trilu2000/HB-CDL-6/Bilder/IMG_20201105_100321.jpg

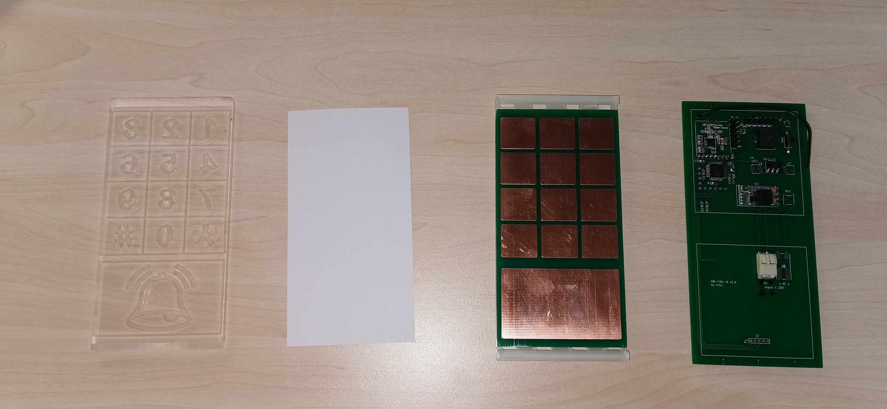
Bilder/IMG_20201105_100321.jpg
