trilu2000/HB-CDL-6/Bilder/IMG_20201105_100423.jpg

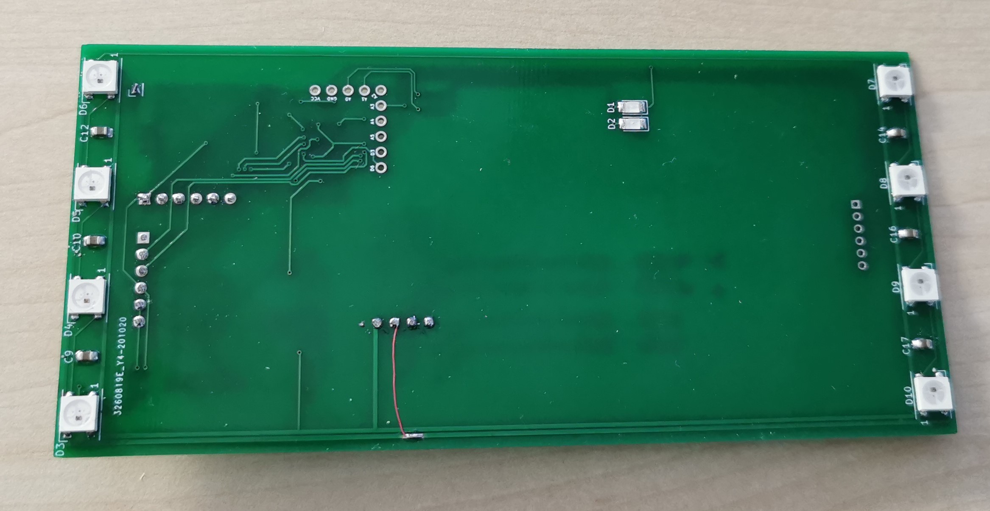
Bilder/IMG_20201105_100423.jpg
