trilu2000/HB-CDL-6/Bilder/IMG_20201105_101753.jpg

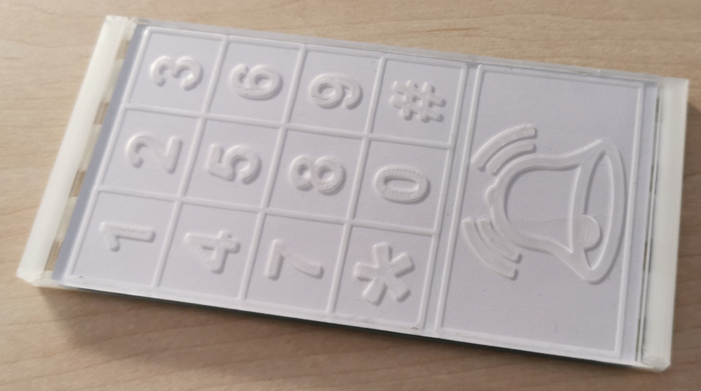
Bilder/IMG_20201105_101753.jpg
