trilu2000/HB-CDL-6/Bilder/IMG_20201106_141219.jpg

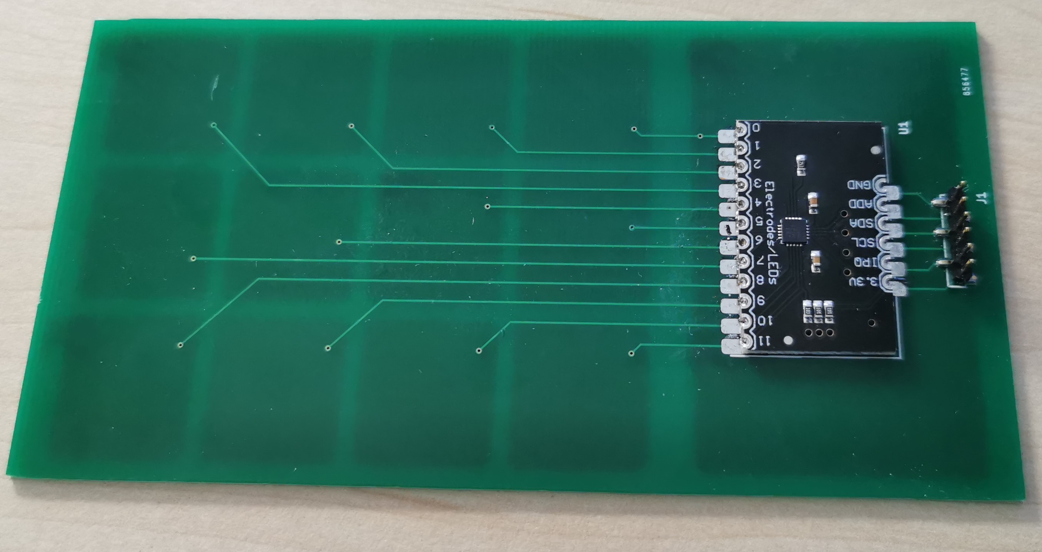
Bilder/IMG_20201106_141219.jpg
