trilu2000/HB-CDL-6/Bilder/IMG_20201106_154348.jpg

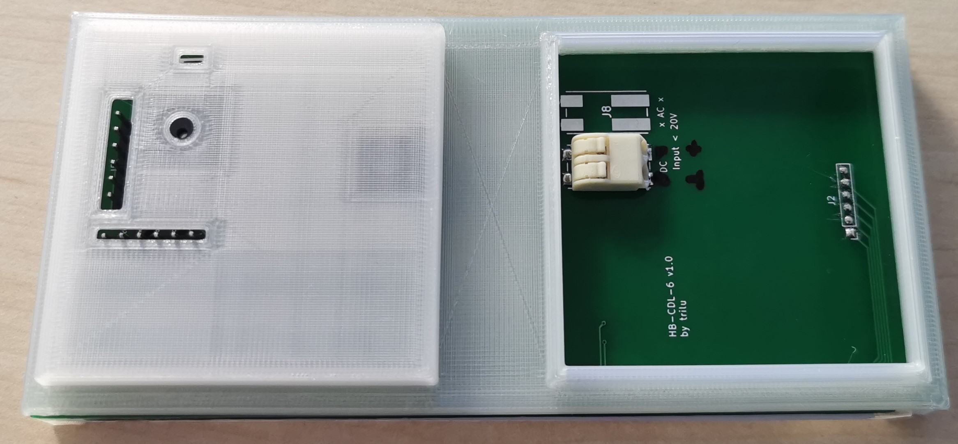
Bilder/IMG_20201106_154348.jpg
