trilu2000/HB-CDL-6/Bilder/IMG_20201106_154539.jpg

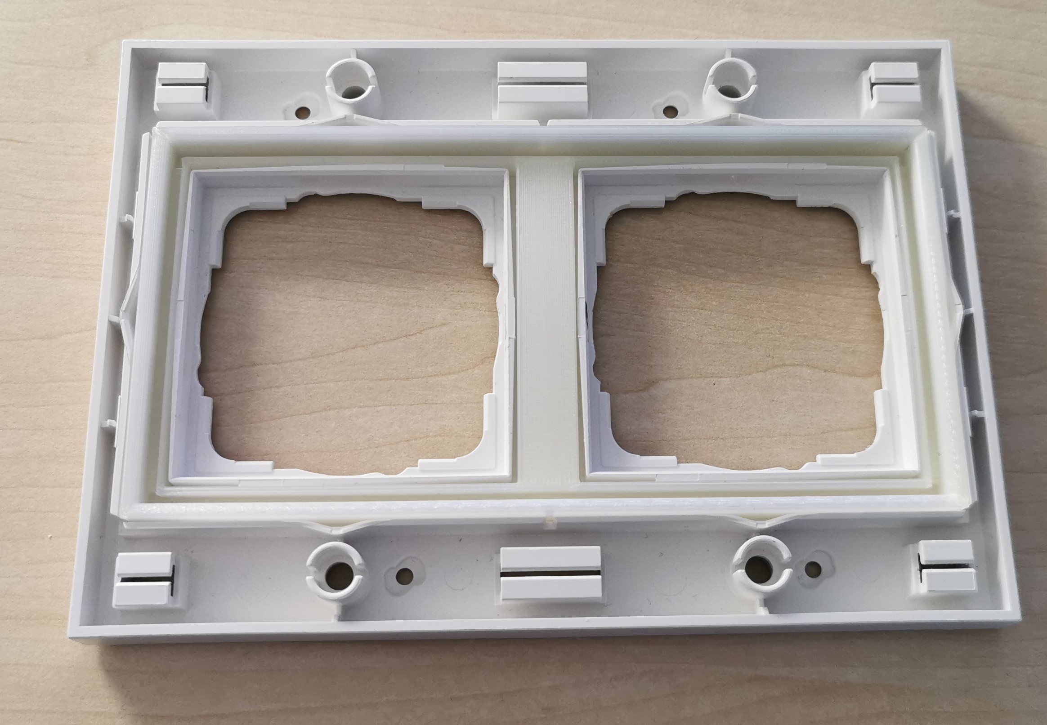
Bilder/IMG_20201106_154539.jpg
