trilu2000/HB-CDL-6/Bilder/IMG_20201109_151858.jpg

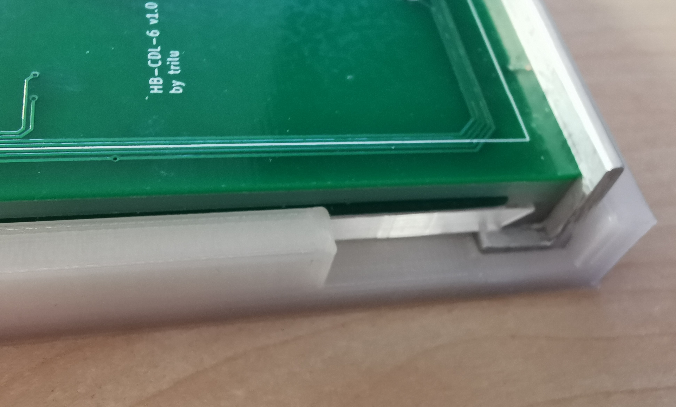
Bilder/IMG_20201109_151858.jpg
