trilu2000/HB-CDL-6/Bilder/IMG_20201111_110530.jpg

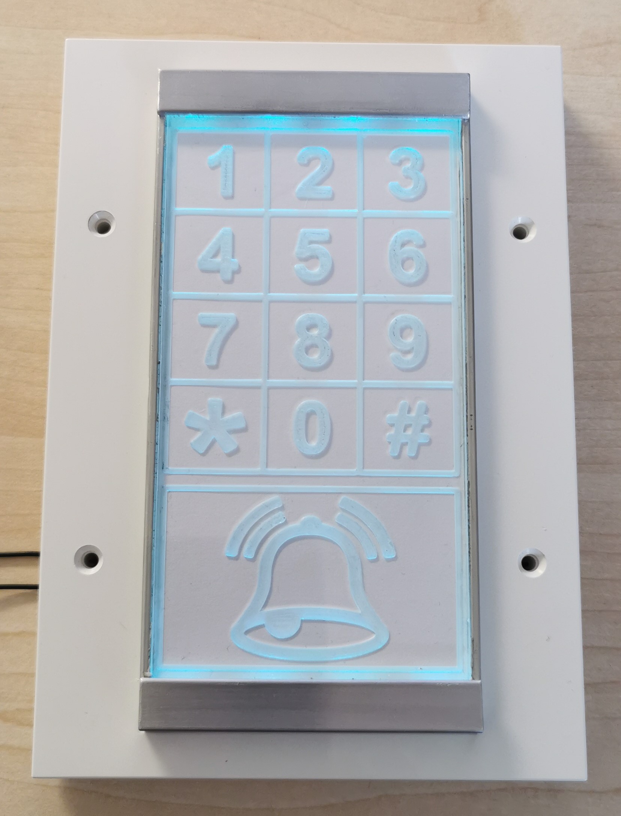
Bilder/IMG_20201111_110530.jpg
