trilu2000/HB-CDL-6/Bilder/Touch-Flaeche-back.png

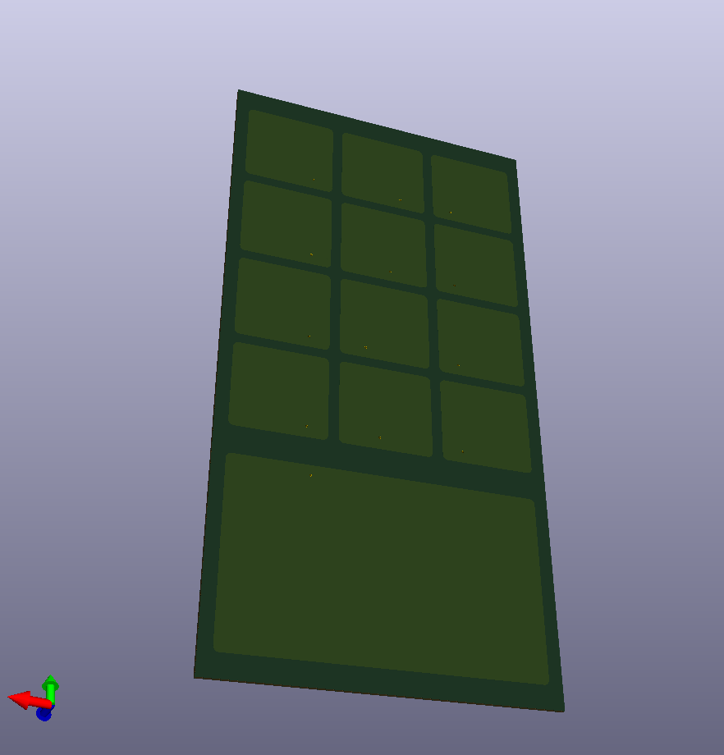
Bilder/Touch-Flaeche-back.png
