trilu2000/HB-CDL-6/Bilder/Touch-Steuerung-back.png

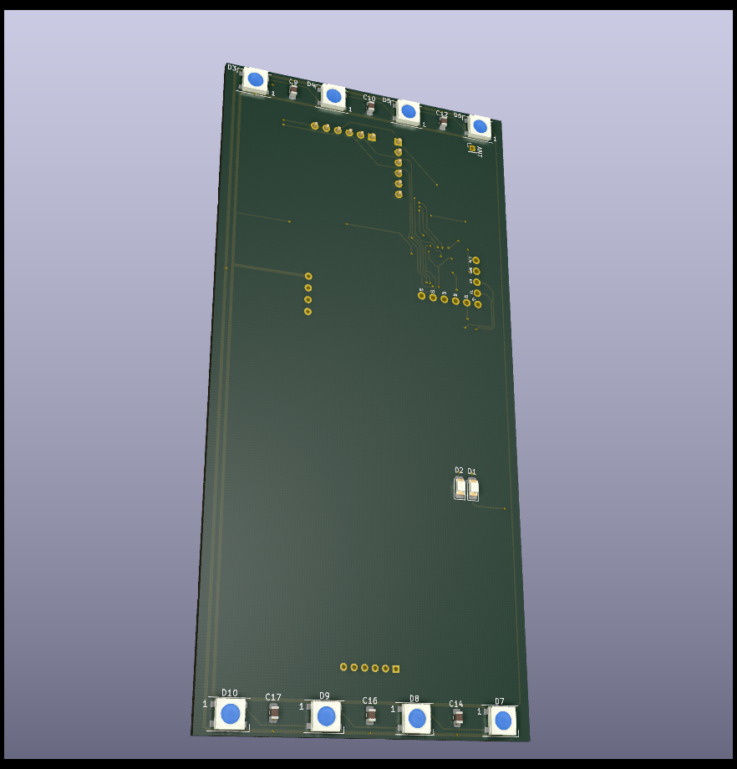
Bilder/Touch-Steuerung-back.png
